alprema/py-clicker/hardware/blue_button.png

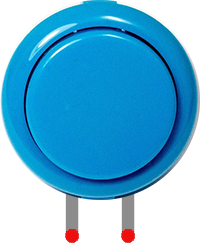
hardware/blue_button.png
