alprema/py-clicker/hardware/charging_module.png

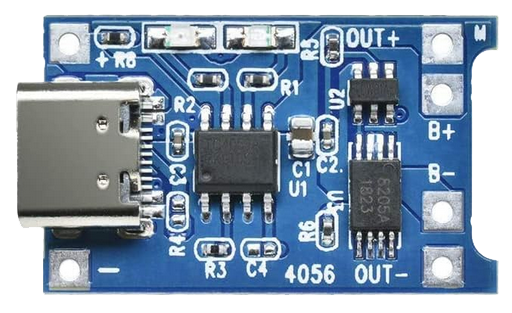
hardware/charging_module.png
