alprema/py-clicker/hardware/power_converter.png

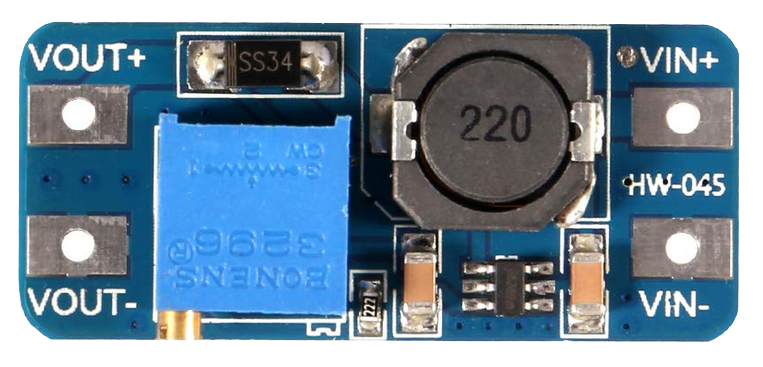
hardware/power_converter.png
