alprema/py-clicker/hardware/raspberry_pi_zero_w.png

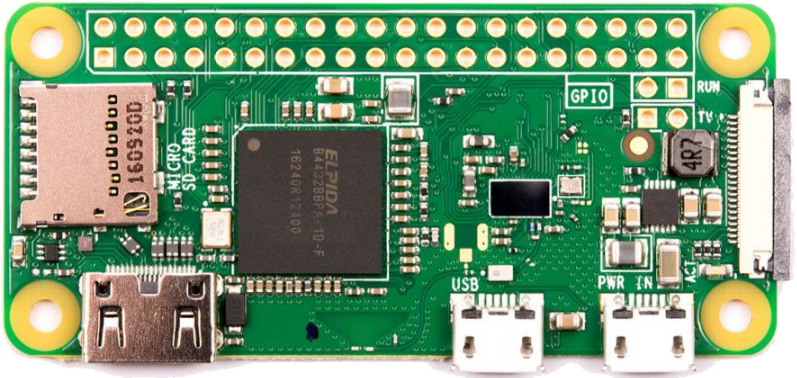
hardware/raspberry_pi_zero_w.png
