alprema/py-clicker/hardware/raspberry_pi_zero_w_ports_mask.png

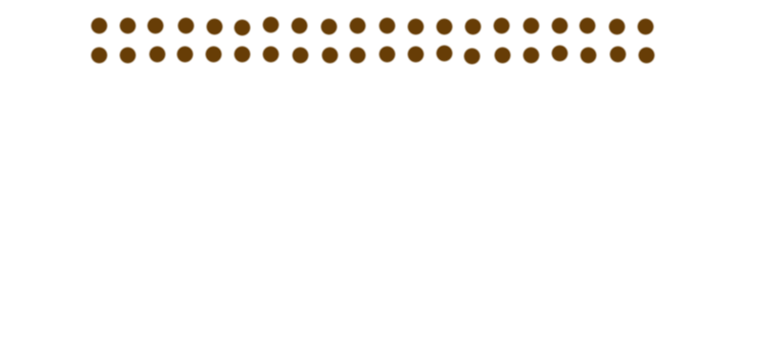
hardware/raspberry_pi_zero_w_ports_mask.png
